electgpl/AmplificadorClaseA/Imagenes/20181019_105909.jpg

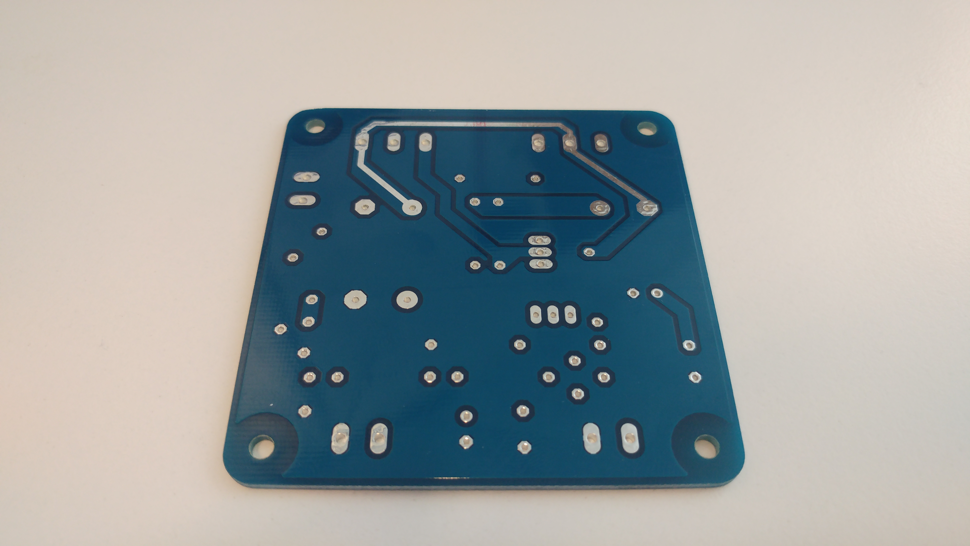
Imagenes/20181019_105909.jpg
