electgpl/AmplificadorClaseA/Analisis/Amplificador_Clase_A.asc

C1: cap; 0.1µ; V=16 Irms=1.78 Rser=0.0675534 Lser=0 mfg="KEMET" pn="C1210F104K4RAC" type="X7R"
C2: polcap; 100µ; V=16 Irms=135m Rser=0.8 Lser=0 mfg="Nichicon" pn="UPR1C101MPH" type="Al electrolytic"
C3: cap; 0.47µ; V=16 Irms=0 Rser=0 Lser=0 mfg="Murata" pn="GRM033R61C103KA12" type="X5R"
C4: polcap; 470µ; V=16 Irms=770m Rser=0.09 Lser=0 mfg="Nichicon" pn="UPL1C471MPH6" type="Al electrolytic"
C5: polcap; 220µ; V=16 Irms=460m Rser=0.16 Lser=0 mfg="Nichicon" pn="UPL1C221MPH" type="Al electrolytic"
C6: polcap; 4700µ; V=16 Irms=2.68 Rser=0.02 Lser=0 mfg="Nichicon" pn="UPL1C472MRH" type="Al electrolytic"
C7: cap; 0.1µ; V=16 Irms=728m Rser=0.14361 Lser=0 mfg="KEMET" pn="C0603C104K4RAC" type="X7R"
Q1: pnp; 2N3906
Q2: npn; 2SD1898
Q3: npn; 2N3055
Q4: npn; 2N3055
R1: res; 47k; pwr=0.5
R2: res; 100k; pwr=0.5
R3: res; 100k; pwr=0.5
R4: res; 10k; pwr=0.5
R5: res; 47; pwr=0.5
R6: res; 2.7k; pwr=0.5
R7: res; 220; pwr=0.5
R8: res; 220; pwr=0.5
R9: res; 2.2k; pwr=0.5
R10: res; 10k; pwr=0.5
R11: res; 4.7; pwr=0.5
R12: res; 8; pwr=10
V1: voltage; SINE(0 0.30 1000); AC 0.3
V2: voltage; 12
Named nets: 0
.ac oct 100 1 1000k
